ukmaker/VDPtoTFT/images/IMG_0757.JPG

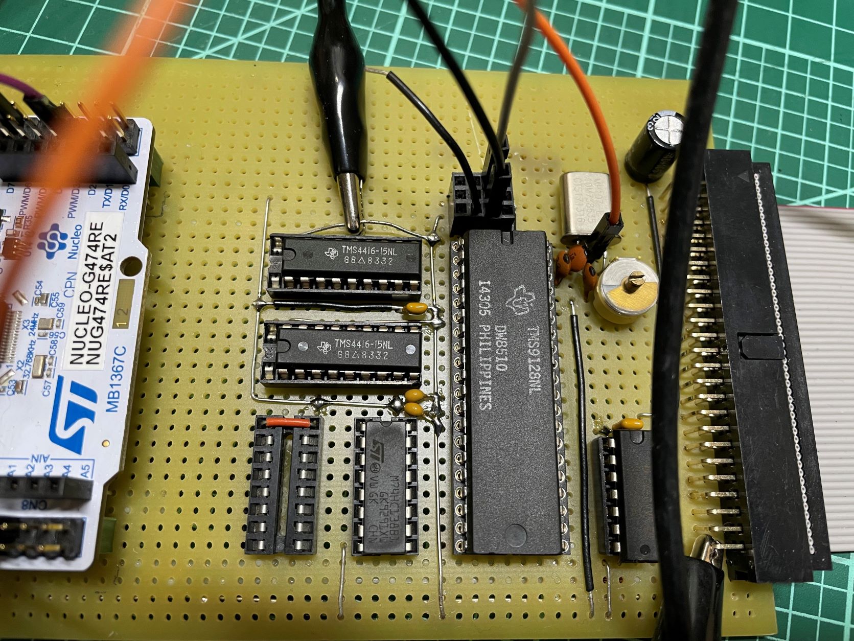
images/IMG_0757.JPG
