ukmaker/VDPtoTFT/images/IMG_0758.JPG

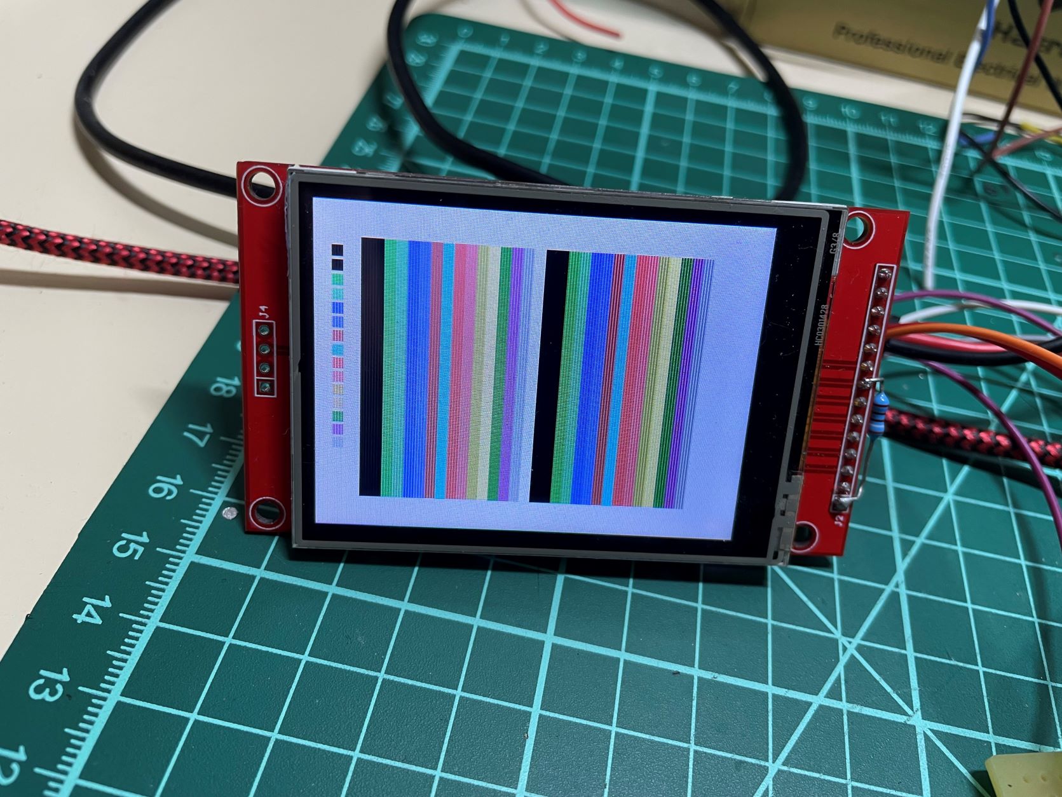
images/IMG_0758.JPG
