ukmaker/VDPtoTFT/images/IMG_0759.JPG

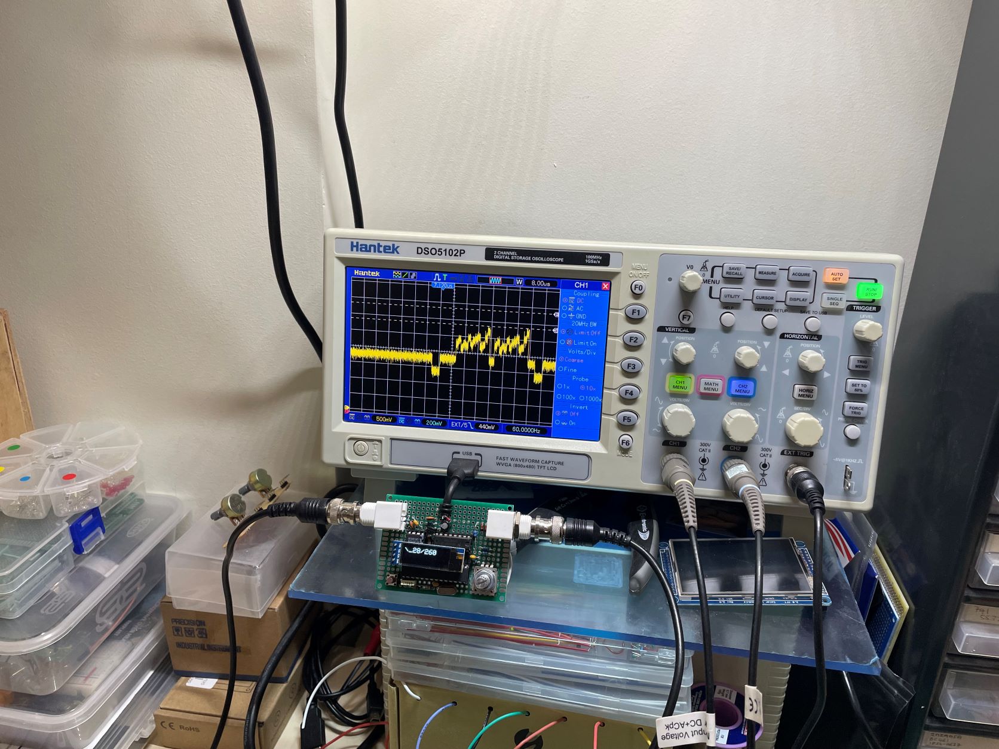
images/IMG_0759.JPG
