ukmaker/VDPtoTFT/images/IMG_0761.JPG

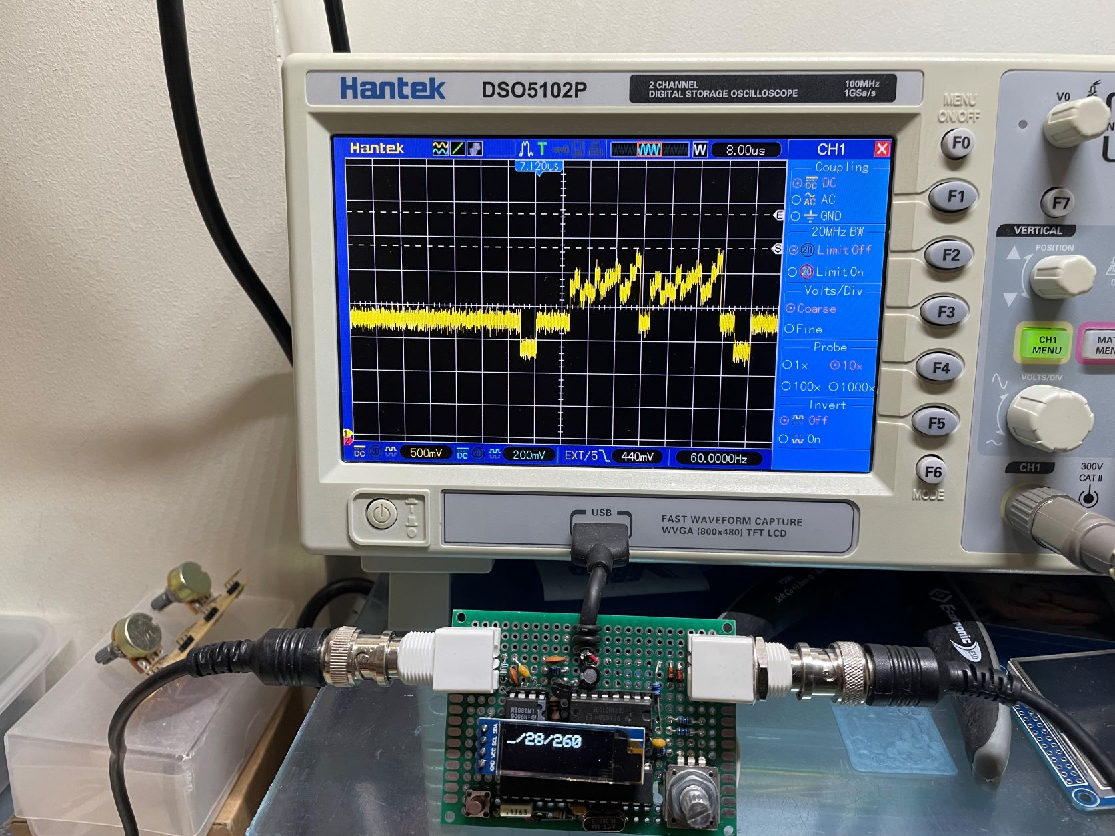
images/IMG_0761.JPG
