ukmaker/VDPtoTFT/images/IMG_0762.JPG

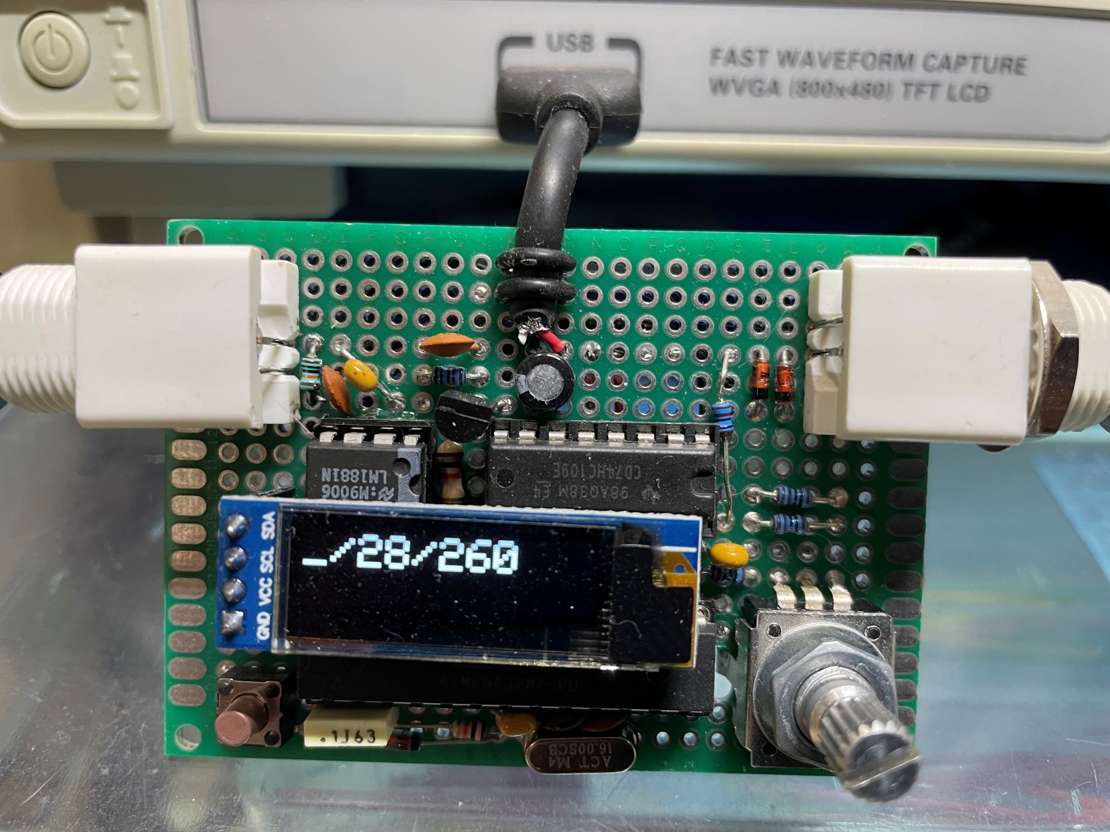
images/IMG_0762.JPG
