ukmaker/VDPtoTFT/images/IMG_0763.JPG

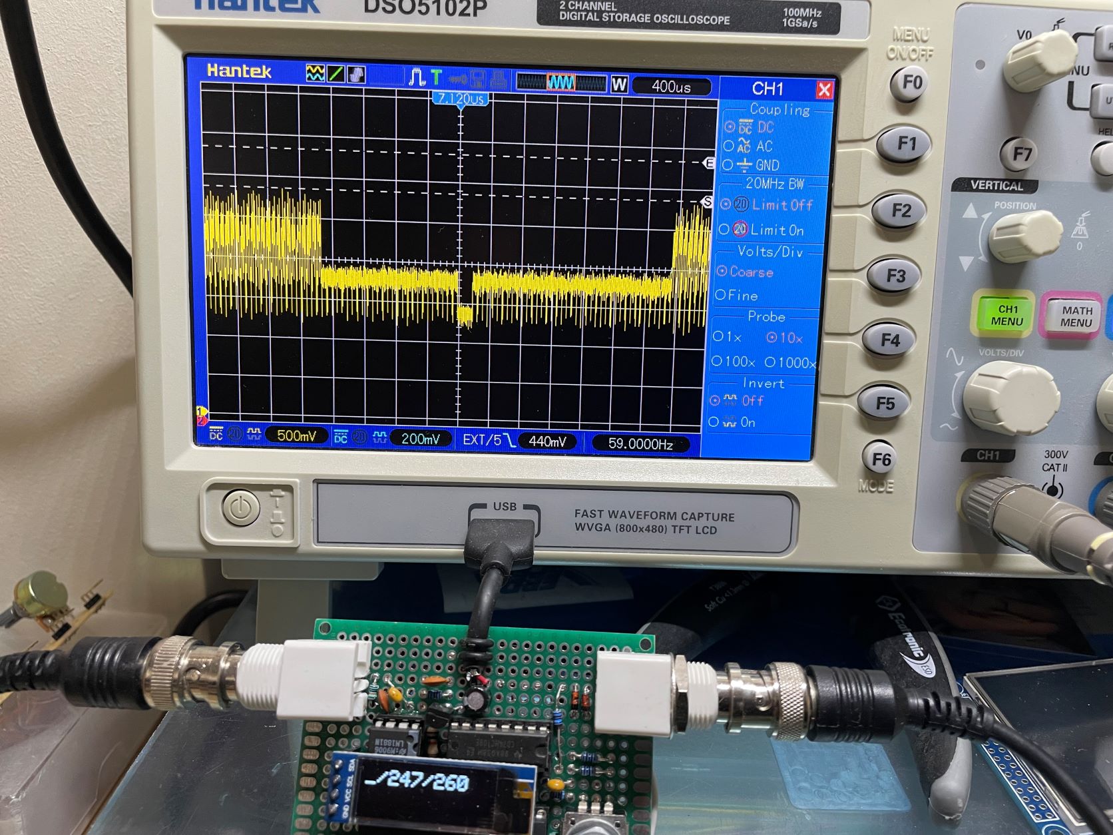
images/IMG_0763.JPG
