ukmaker/VDPtoTFT/images/IMG_0764.JPG

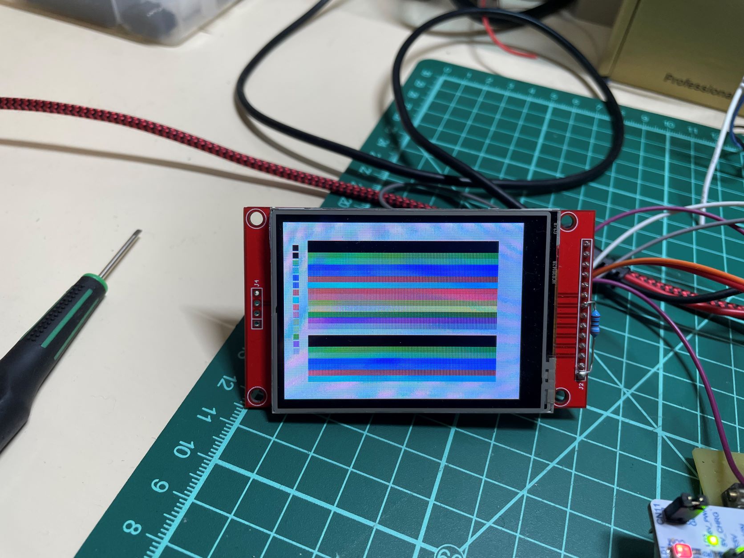
images/IMG_0764.JPG
