ukmaker/VDPtoTFT/images/IMG_0766.JPG

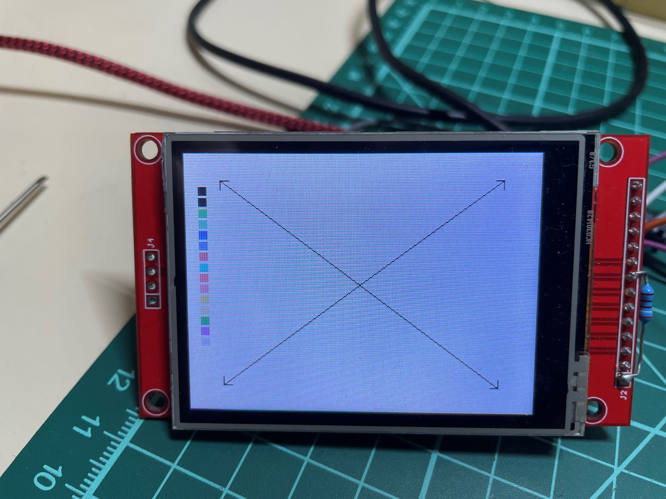
images/IMG_0766.JPG
