ukmaker/VDPtoTFT/images/Sync.PNG

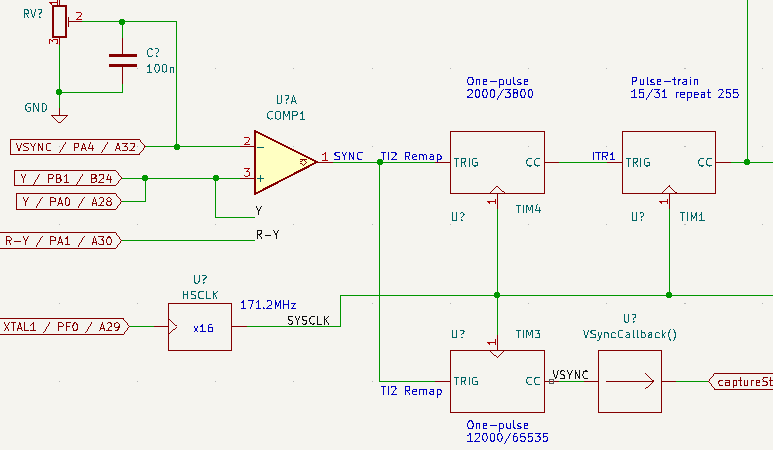
images/Sync.PNG
